Embeetle/tiny-scarab/documentation/website_figures/3d_render_02.webp

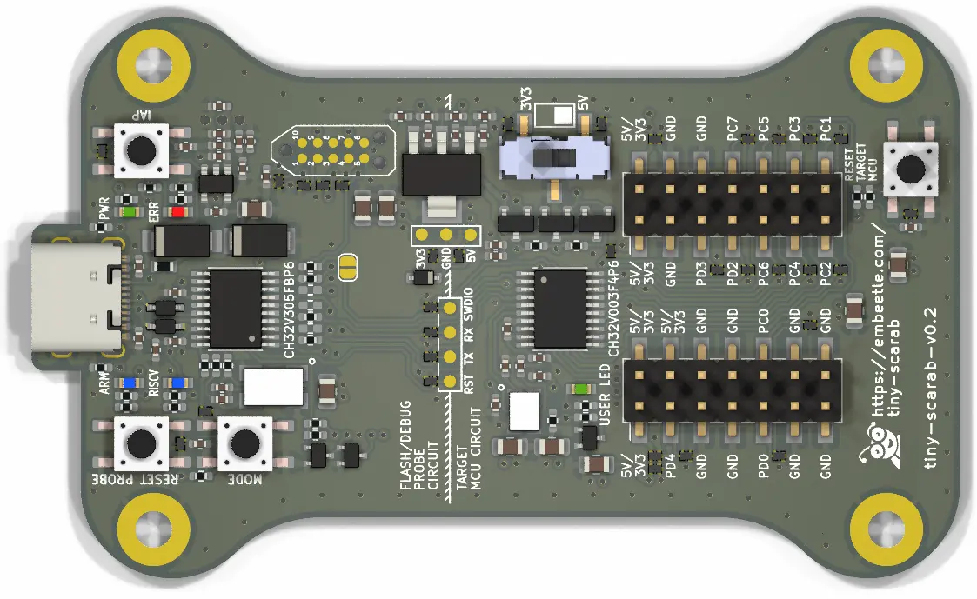
documentation/website_figures/3d_render_02.webp
