Embeetle/tiny-scarab/cardboard_box/box_dimensions.png

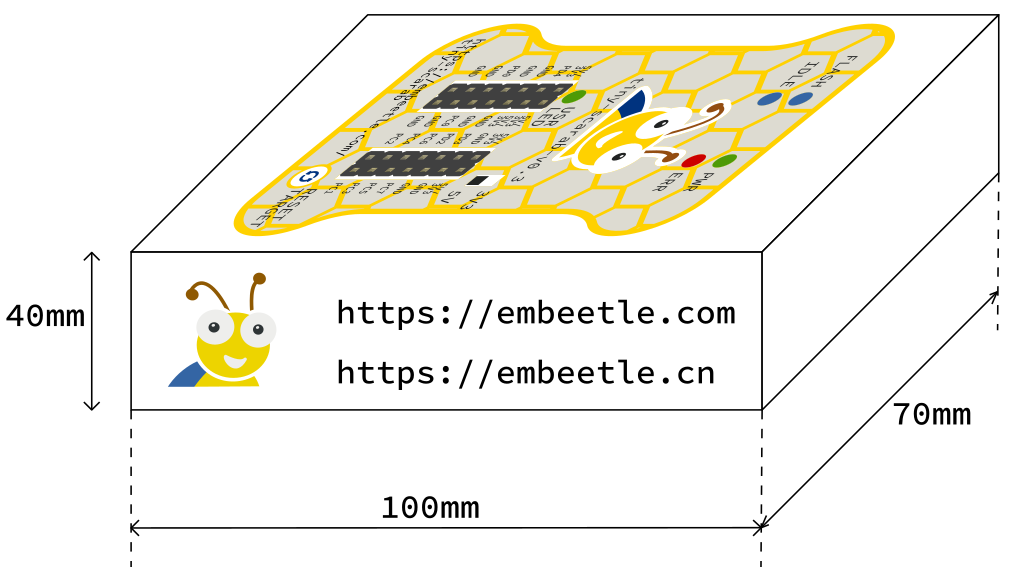
cardboard_box/box_dimensions.png
