Embeetle/tiny-scarab/cardboard_box/product_dimensions.png

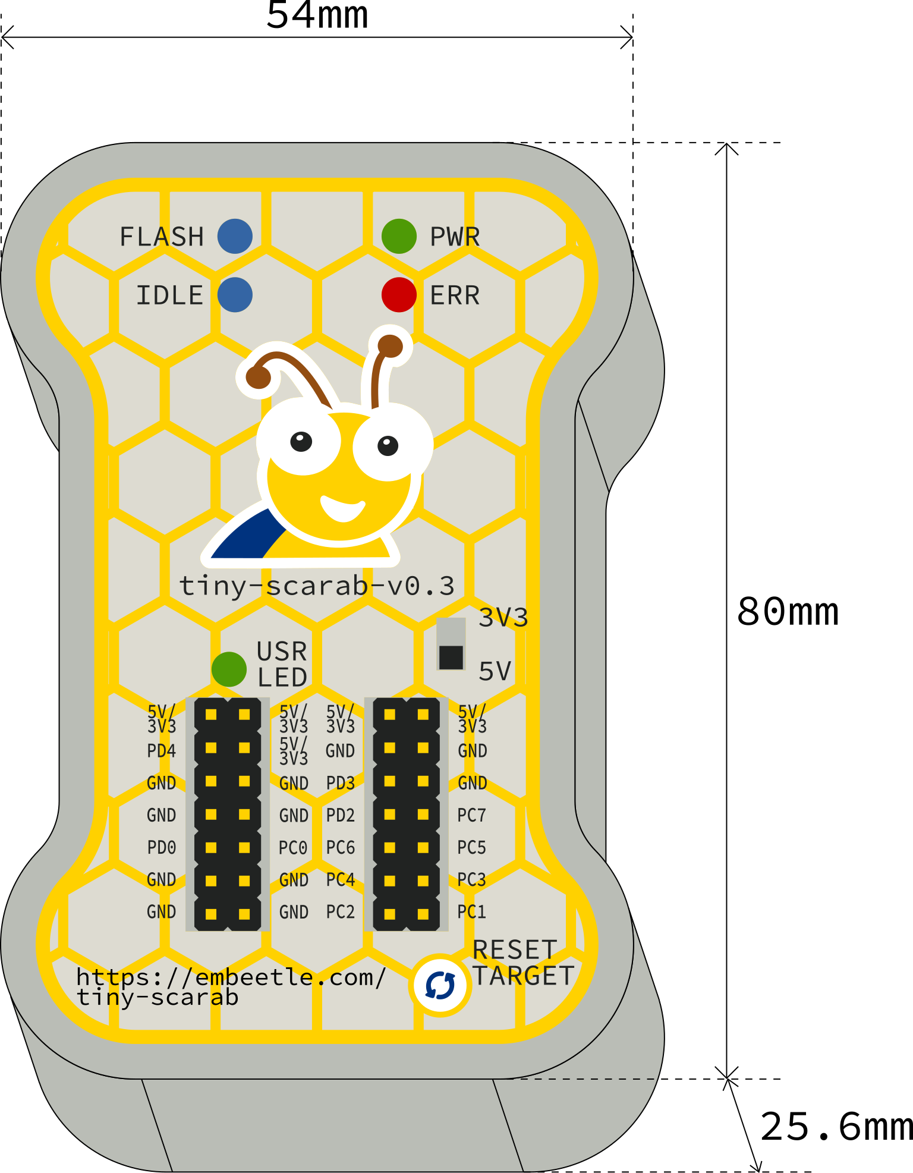
cardboard_box/product_dimensions.png
