Embeetle/tiny-scarab/cardboard_box/product_tree.png

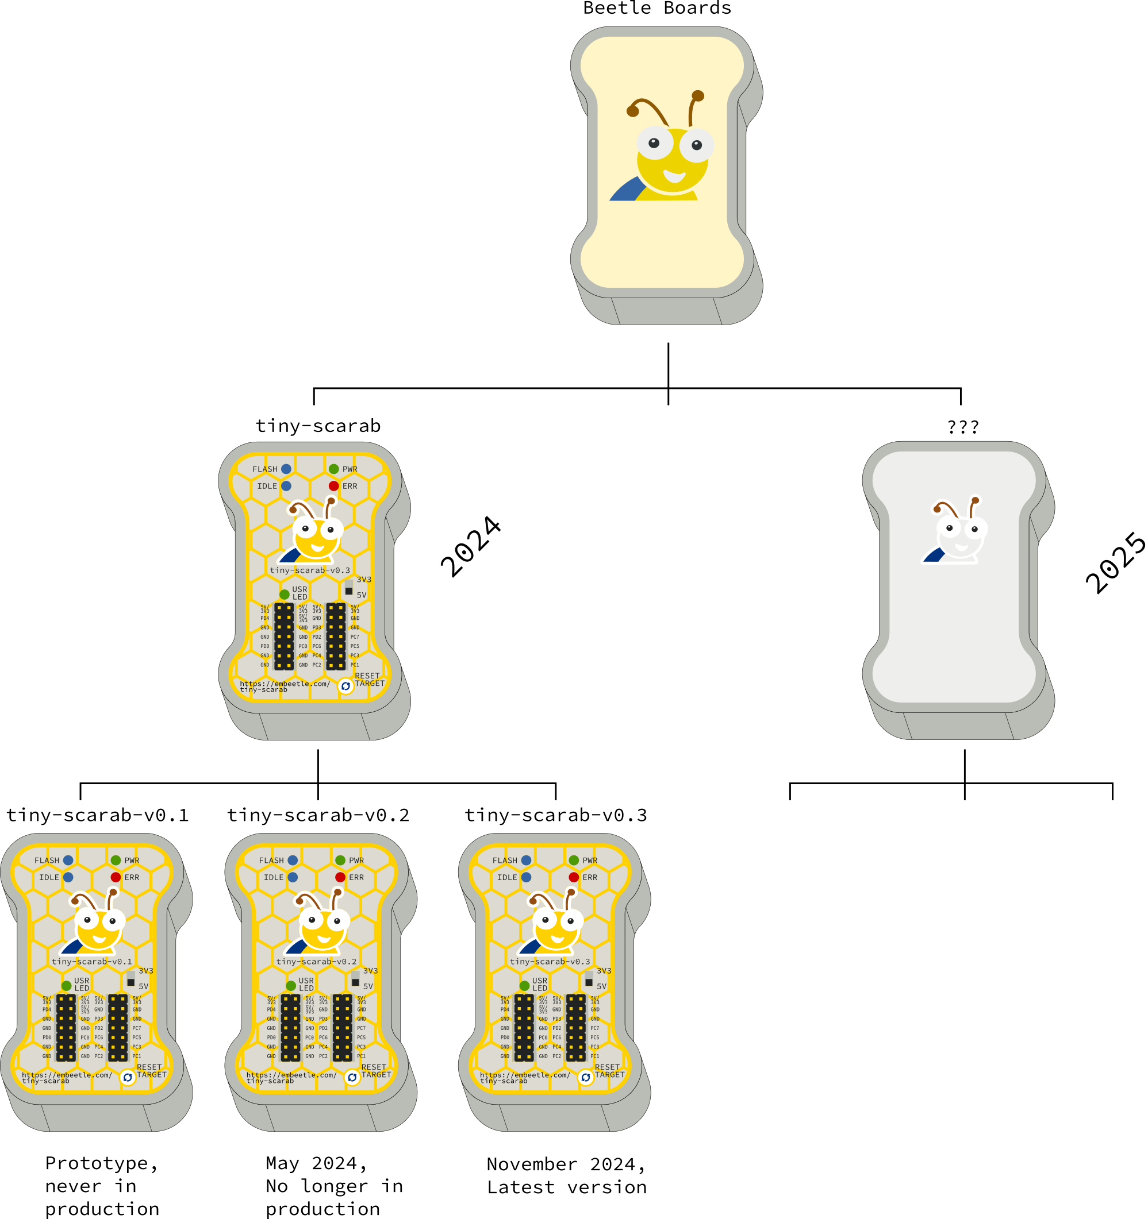
cardboard_box/product_tree.png
