Embeetle/tiny-scarab/cardboard_box/sides.png

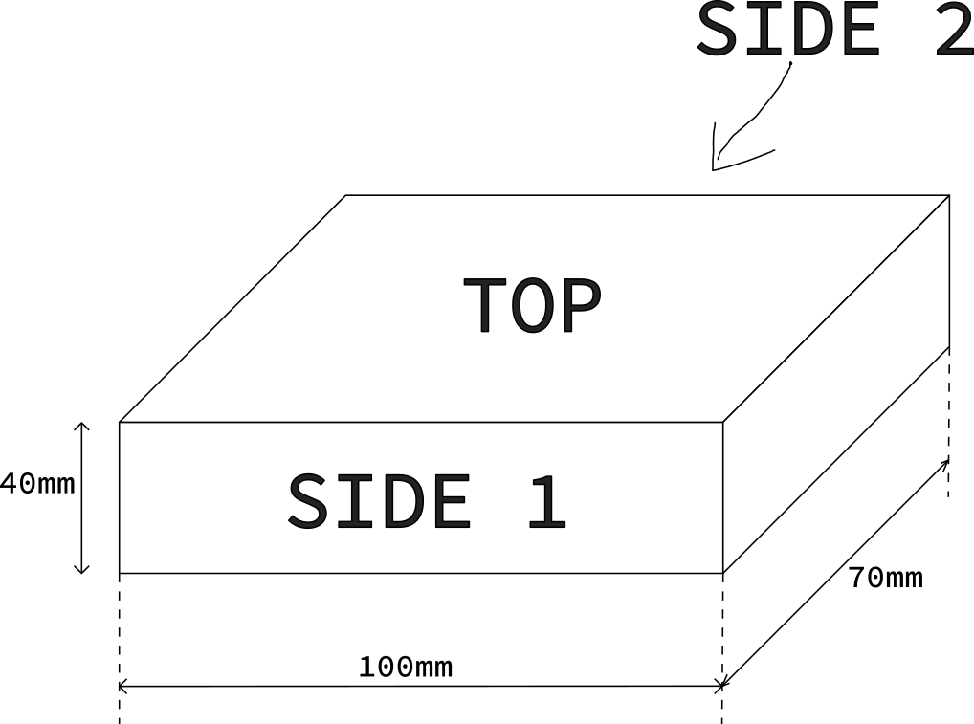
cardboard_box/sides.png
