Embeetle/tiny-scarab/documentation/3d_render_01.png

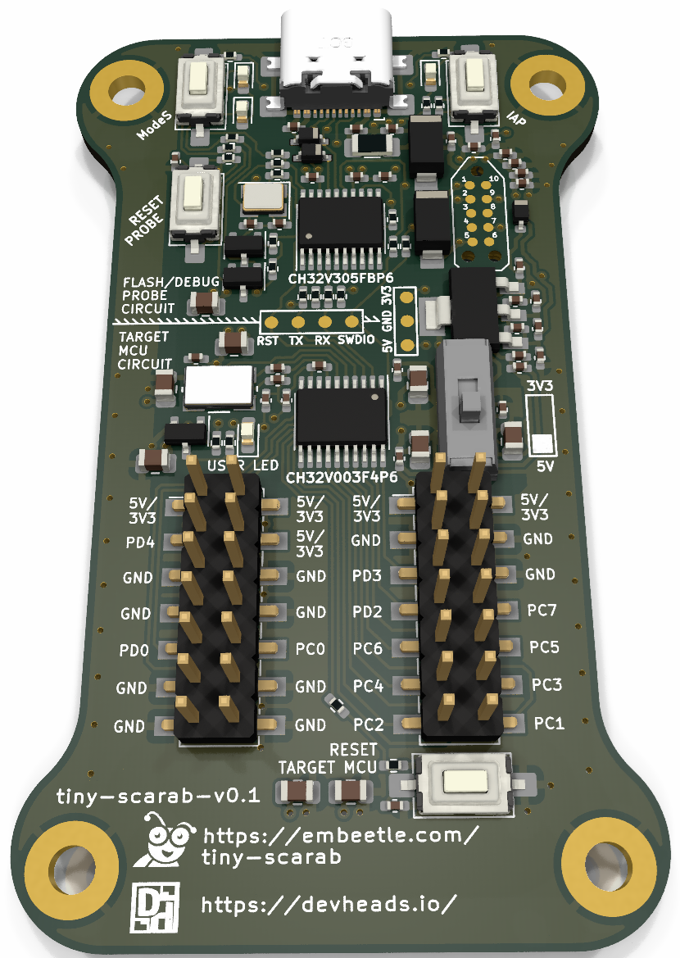
documentation/3d_render_01.png
