Embeetle/tiny-scarab/documentation/3d_render_02.png

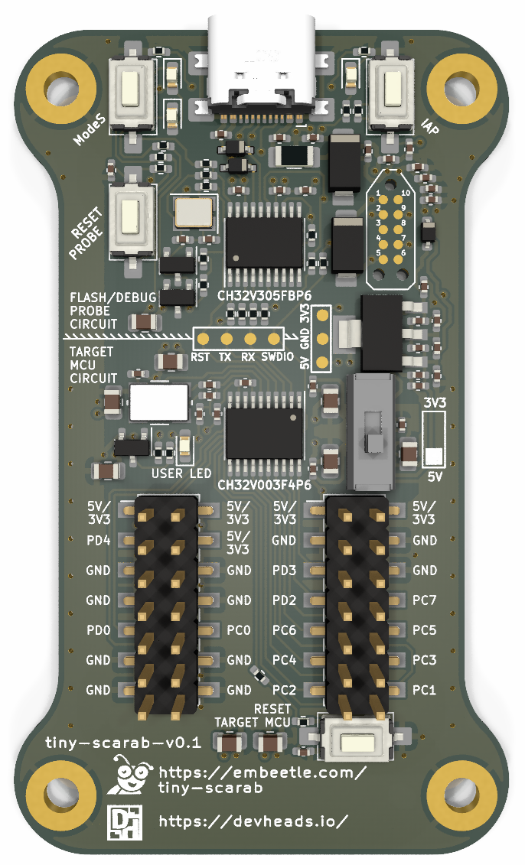
documentation/3d_render_02.png
