Embeetle/tiny-scarab/documentation/back.png

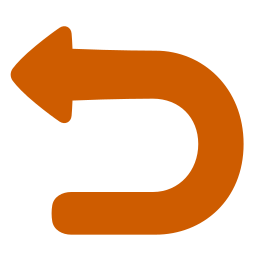
documentation/back.png
