Embeetle/tiny-scarab/documentation/drawing.png

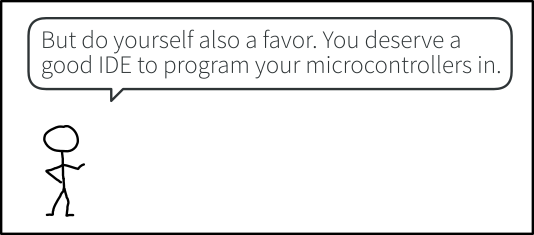
documentation/drawing.png
