Embeetle/tiny-scarab/documentation/esd_discharge_5V.png

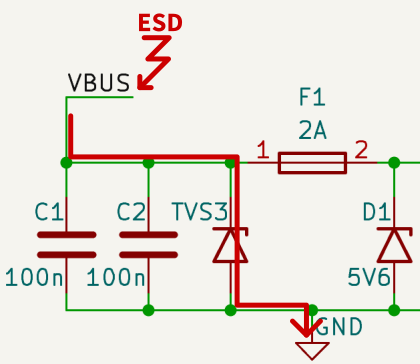
documentation/esd_discharge_5V.png
