Embeetle/tiny-scarab/documentation/files_explained_01.png

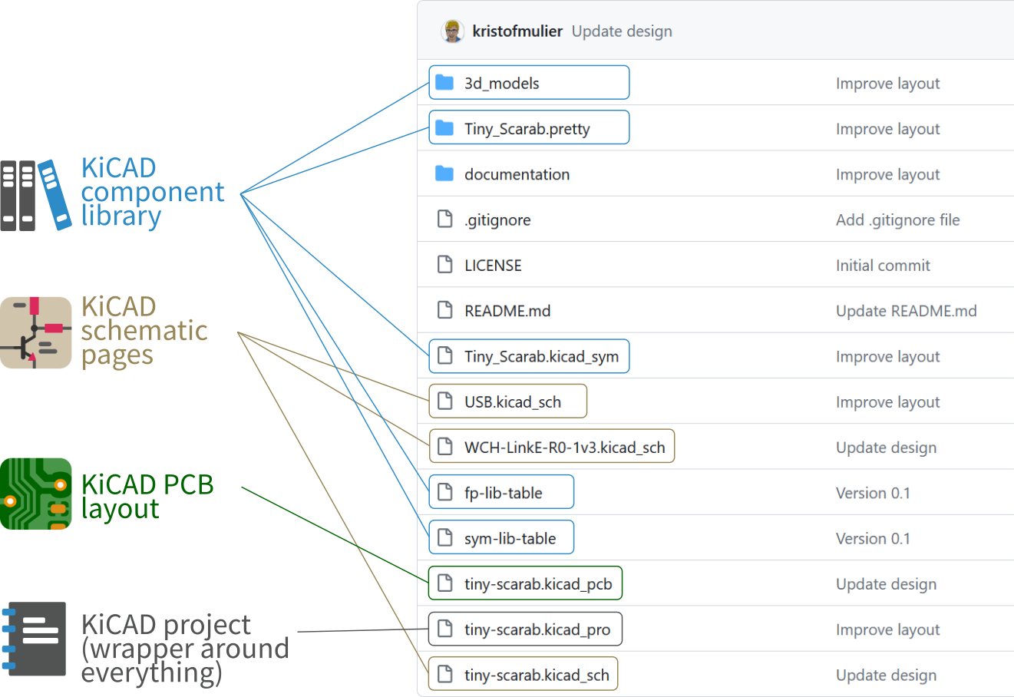
documentation/files_explained_01.png
