Embeetle/tiny-scarab/documentation/home.png

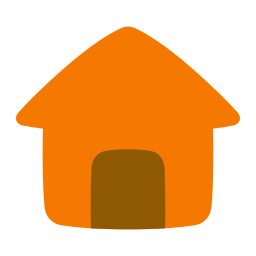
documentation/home.png
