Embeetle/tiny-scarab/documentation/open_project_01.png

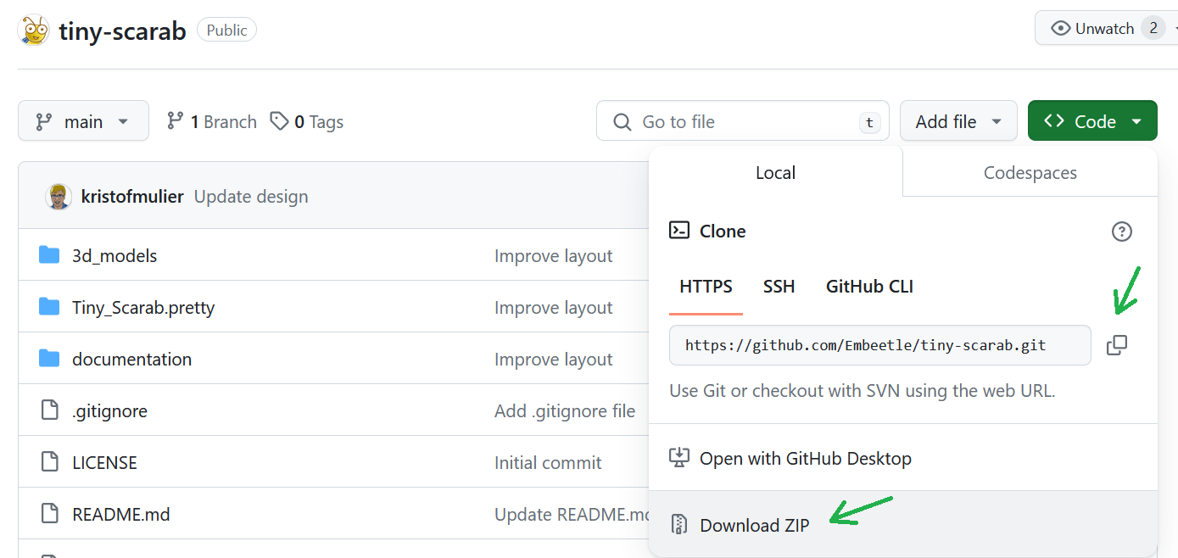
documentation/open_project_01.png
