Embeetle/tiny-scarab/documentation/open_project_02.png

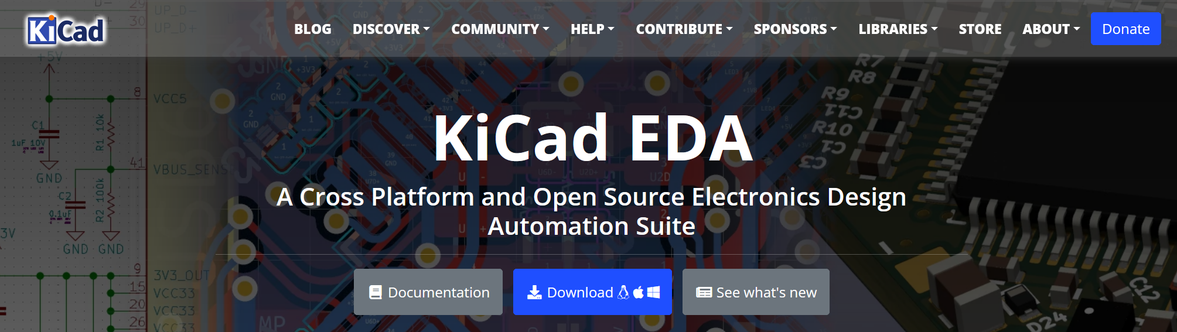
documentation/open_project_02.png
