Embeetle/tiny-scarab/documentation/open_project_03.png

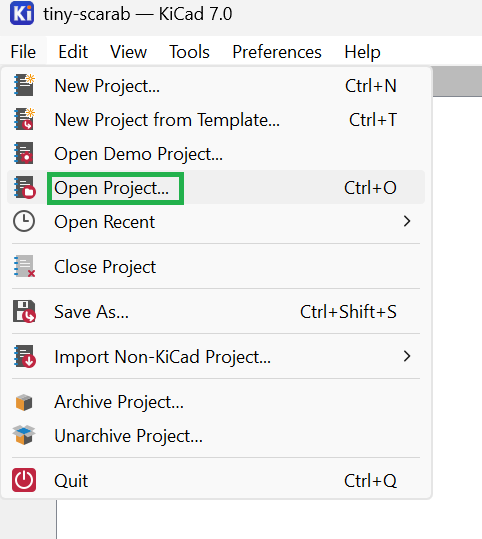
documentation/open_project_03.png
