Embeetle/tiny-scarab/documentation/open_project_04.png

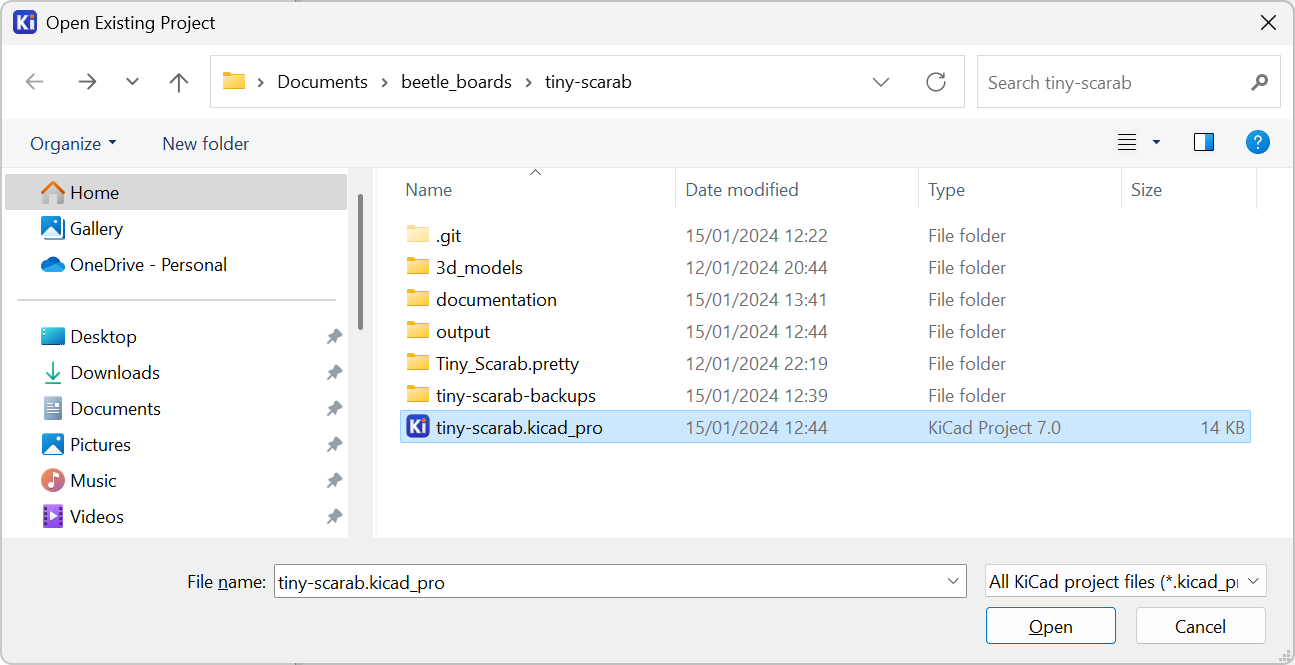
documentation/open_project_04.png
