Embeetle/tiny-scarab/documentation/open_project_05.png

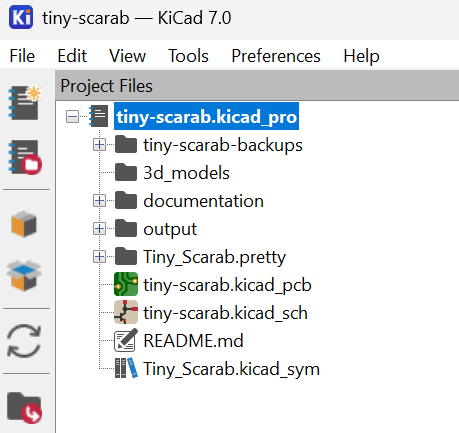
documentation/open_project_05.png
