Embeetle/tiny-scarab/documentation/short_circuit.png

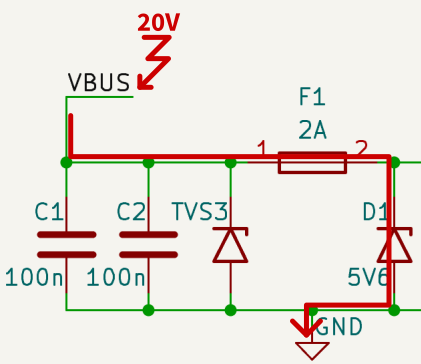
documentation/short_circuit.png
