Embeetle/tiny-scarab/documentation/tiny-scarab.png

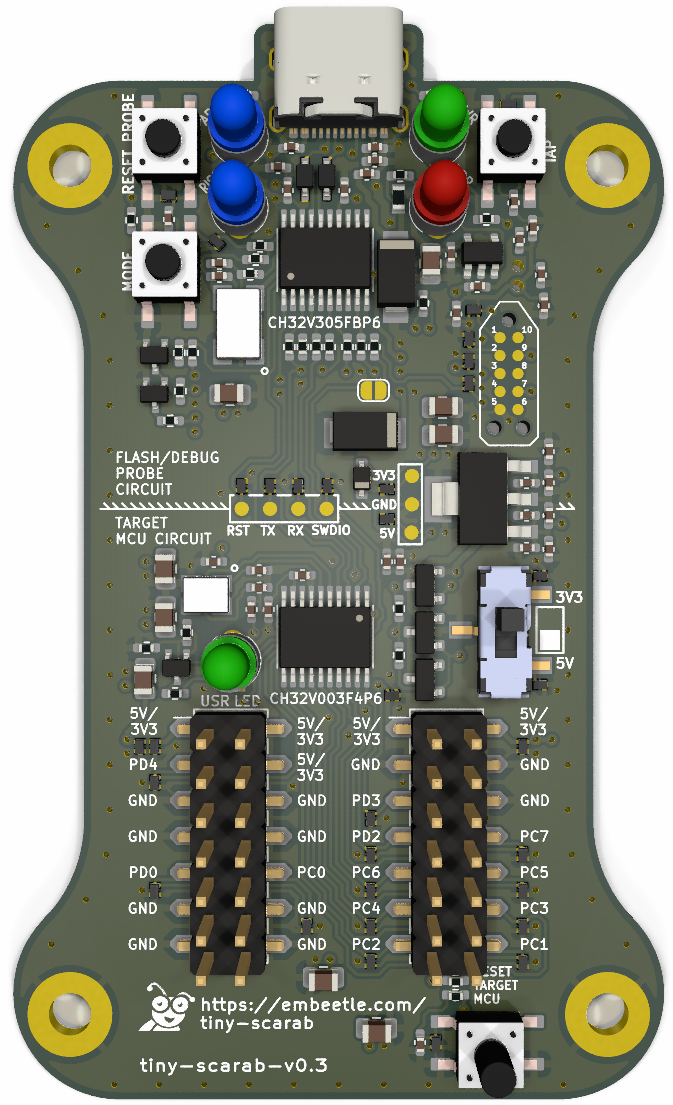
documentation/tiny-scarab.png
