Embeetle/tiny-scarab/documentation/website_figures/3d_render_01.png

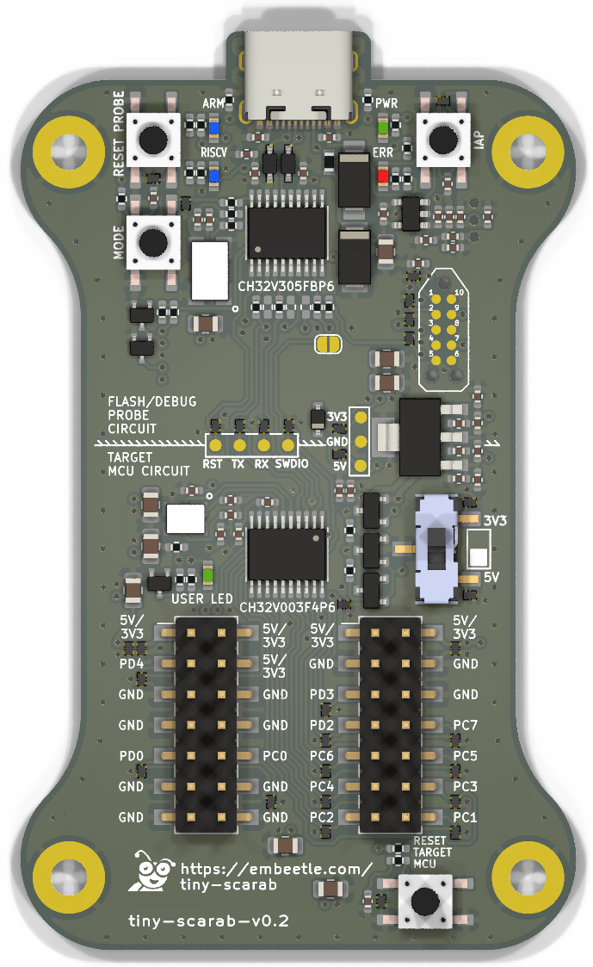
documentation/website_figures/3d_render_01.png
