Embeetle/tiny-scarab/documentation/website_figures/connections_01.webp

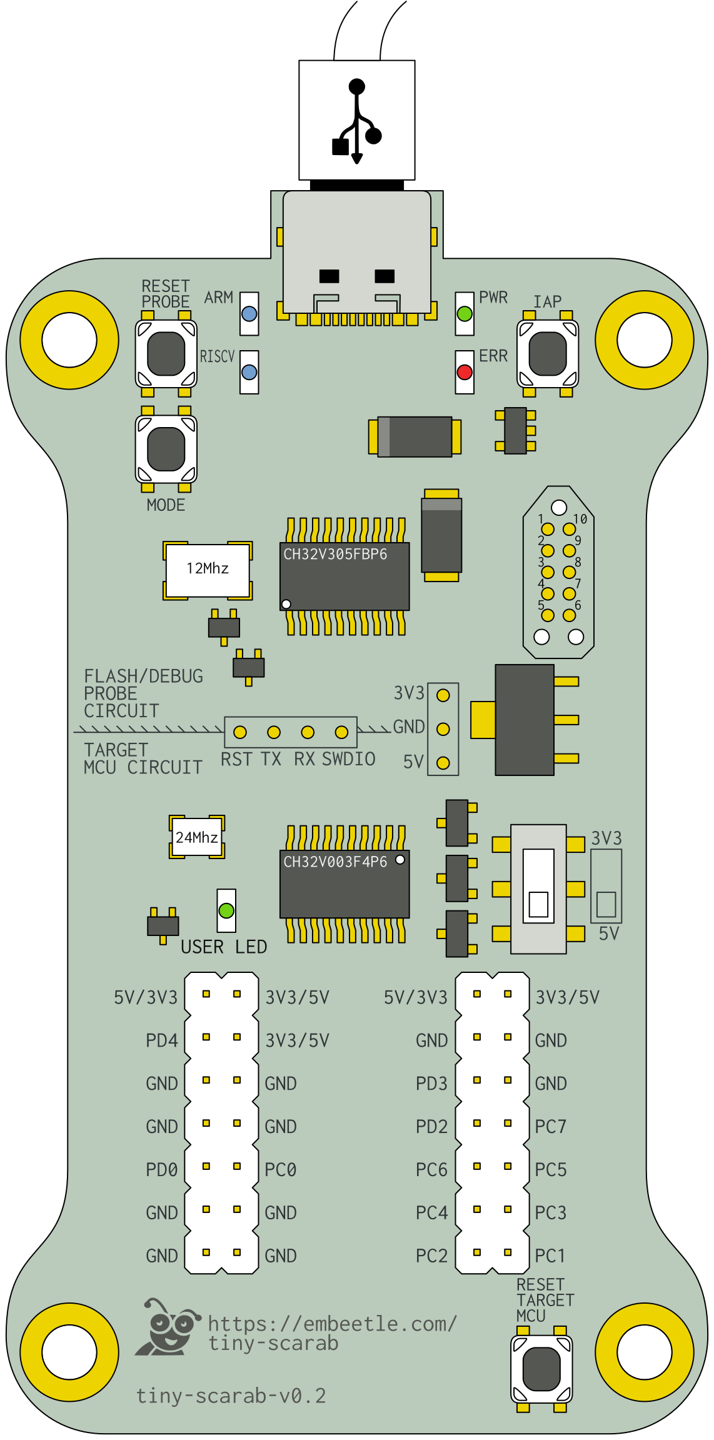
documentation/website_figures/connections_01.webp
