Embeetle/tiny-scarab/documentation/website_figures/mcu_photo.png

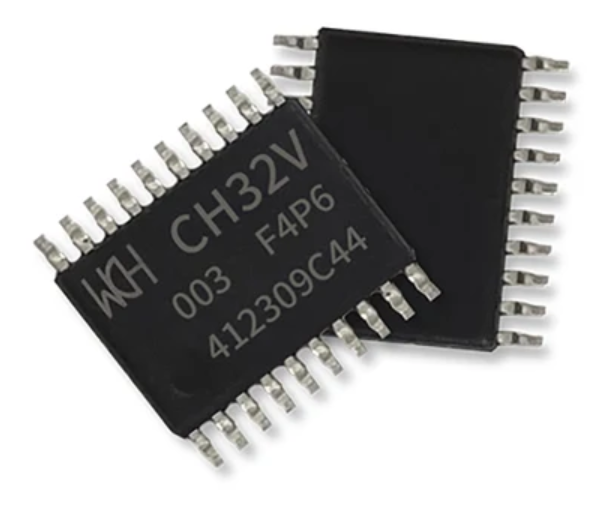
documentation/website_figures/mcu_photo.png
