Embeetle/tiny-scarab/documentation/website_figures/photo_01.webp

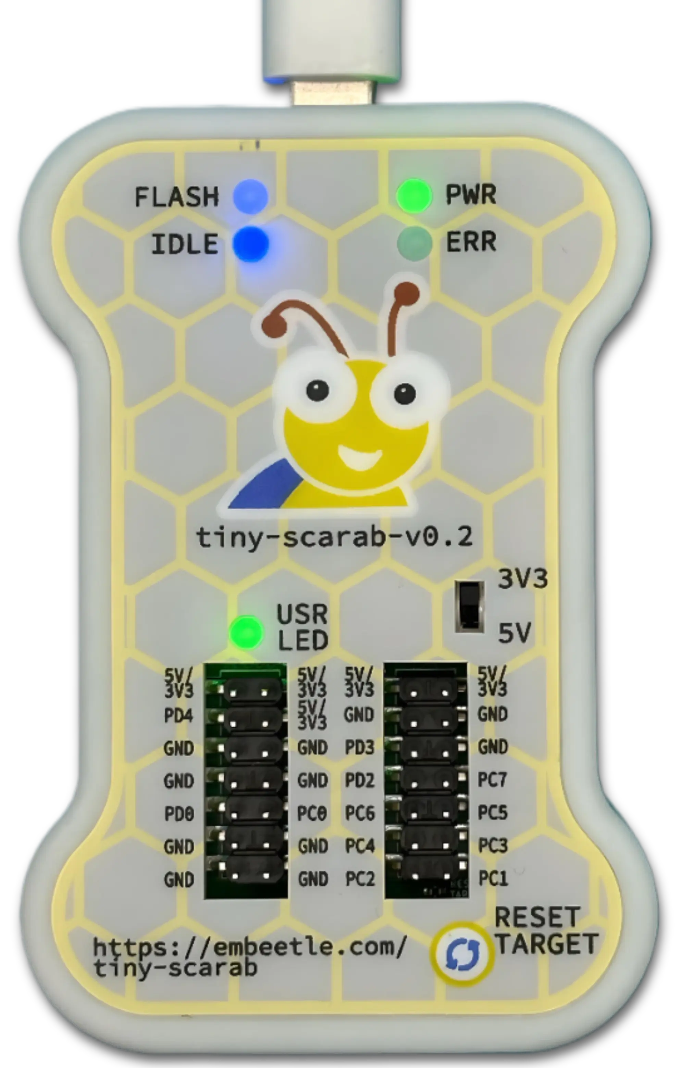
documentation/website_figures/photo_01.webp
