Embeetle/tiny-scarab/documentation/website_figures/photo_02.webp

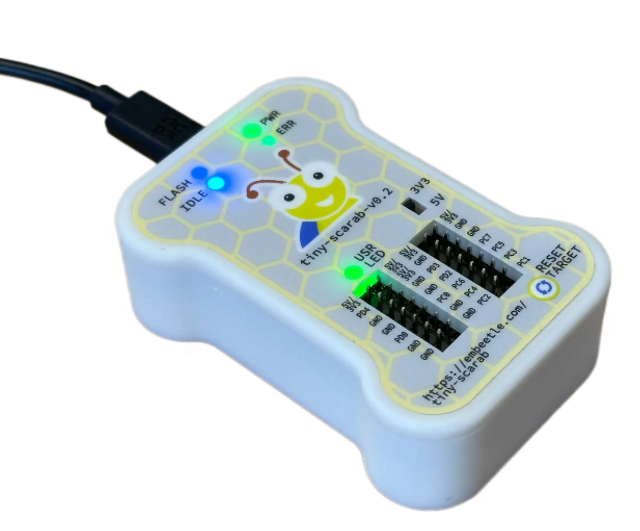
documentation/website_figures/photo_02.webp
