Embeetle/tiny-scarab/documentation/website_figures/photo_03.webp

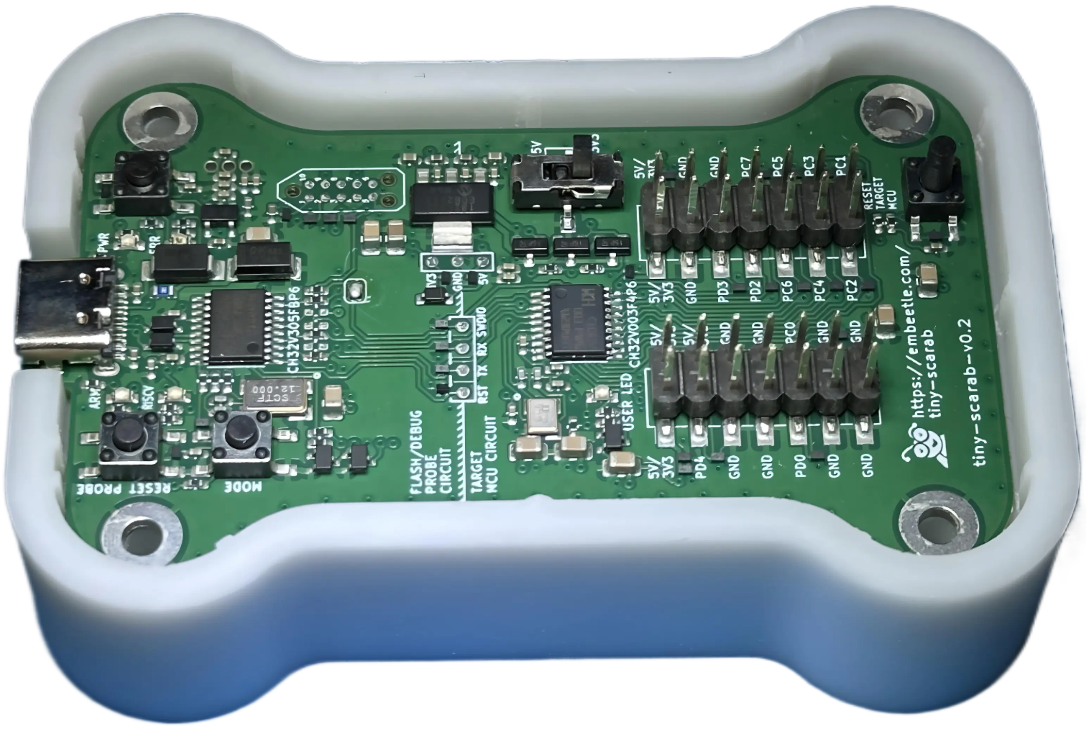
documentation/website_figures/photo_03.webp
