Embeetle/tiny-scarab/documentation/website_figures/photo_04.png

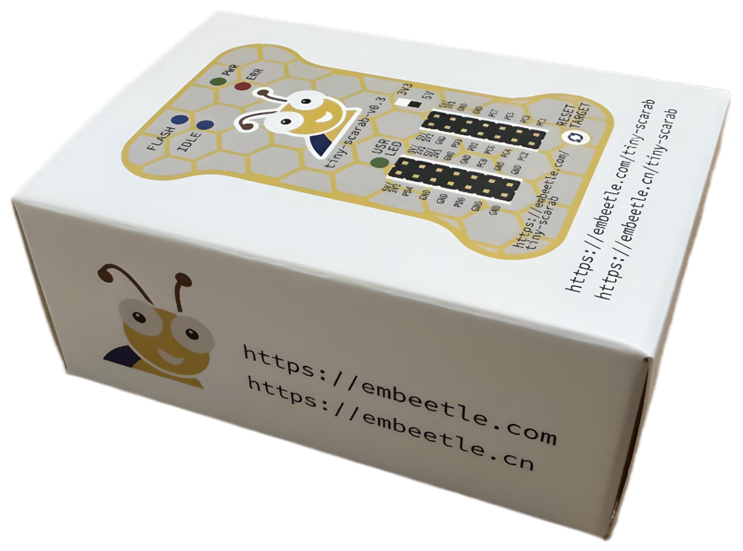
documentation/website_figures/photo_04.png
