Embeetle/tiny-scarab/documentation/website_figures/photo_05.png

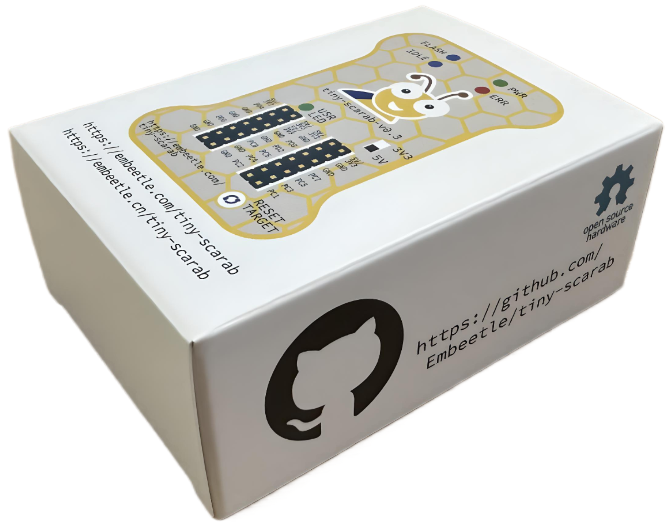
documentation/website_figures/photo_05.png
