Embeetle/tiny-scarab/documentation/website_figures/power_protection_01.png

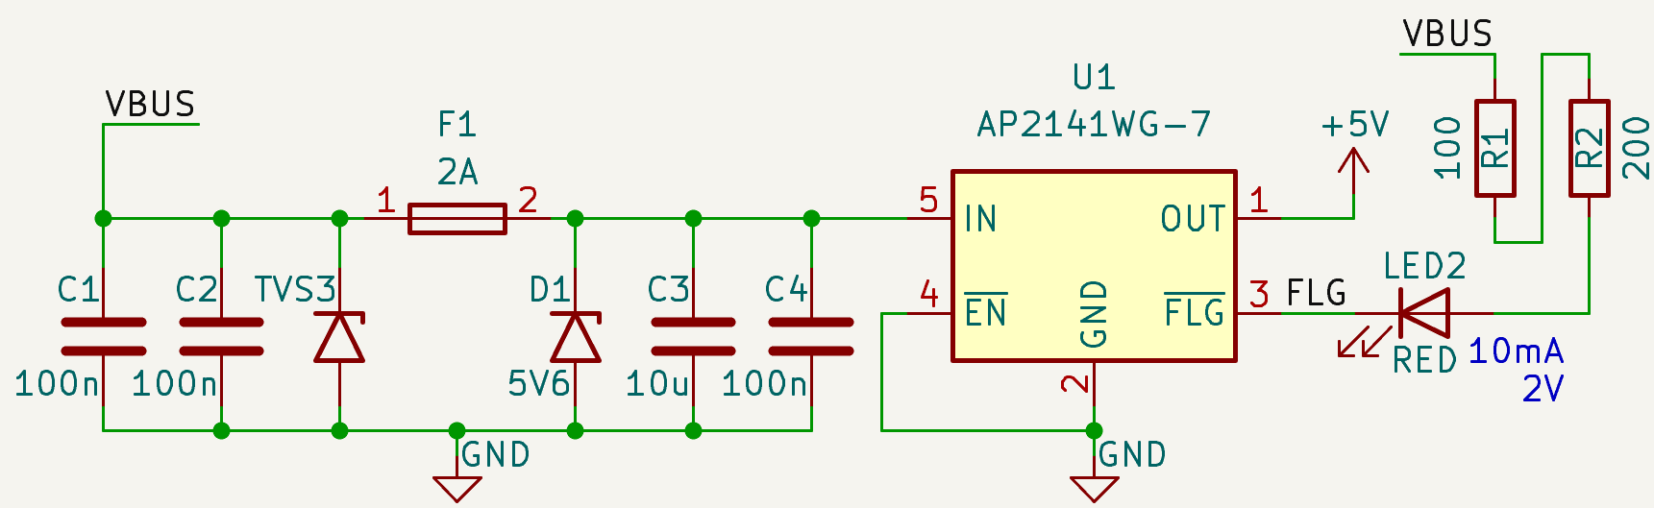
documentation/website_figures/power_protection_01.png
