Embeetle/tiny-scarab/documentation/website_figures/screenshot.png

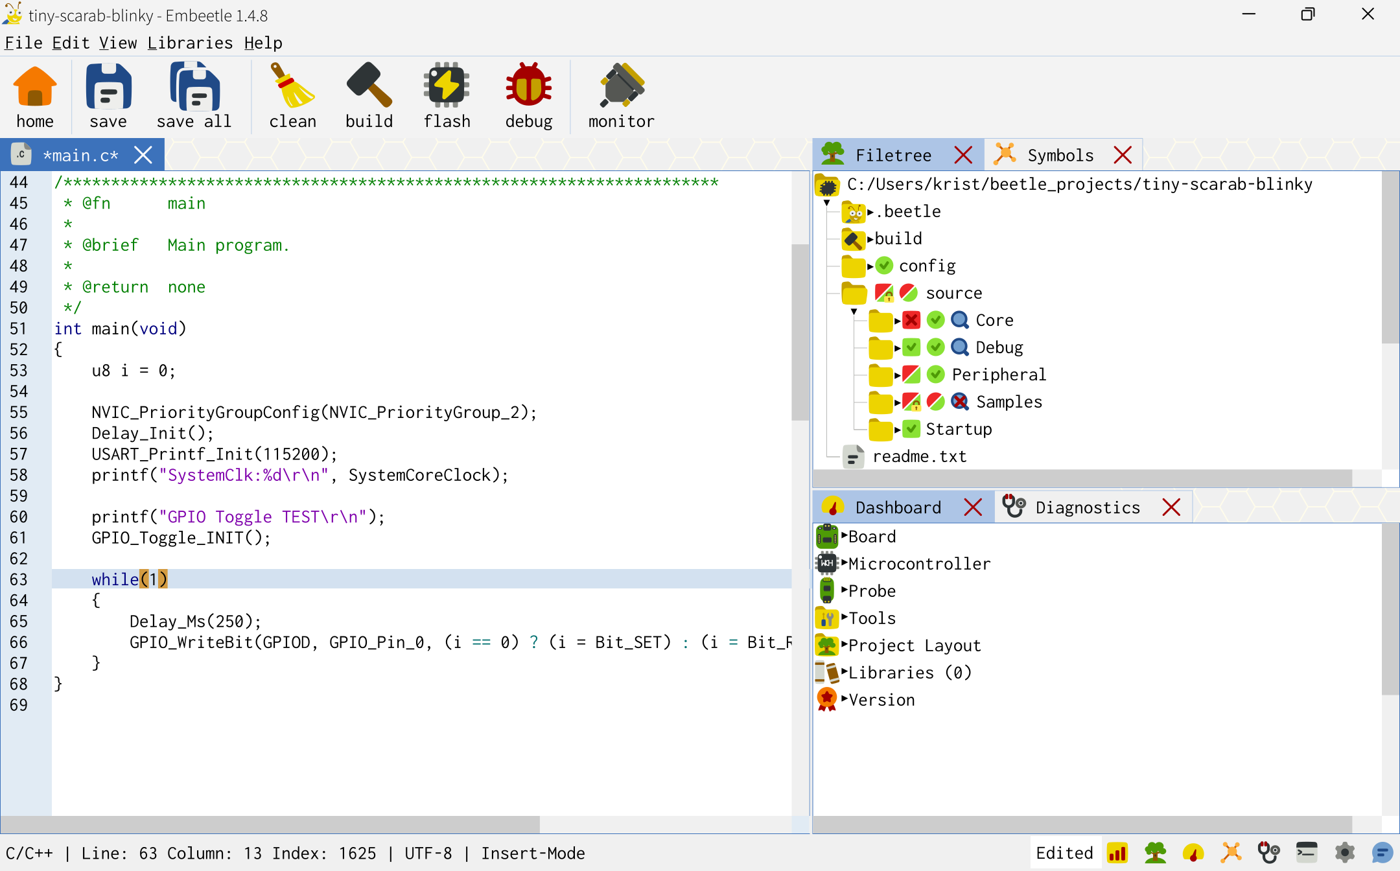
documentation/website_figures/screenshot.png
