Embeetle/tiny-scarab/documentation/website_figures/tiny_scarab_with_screenshot.png

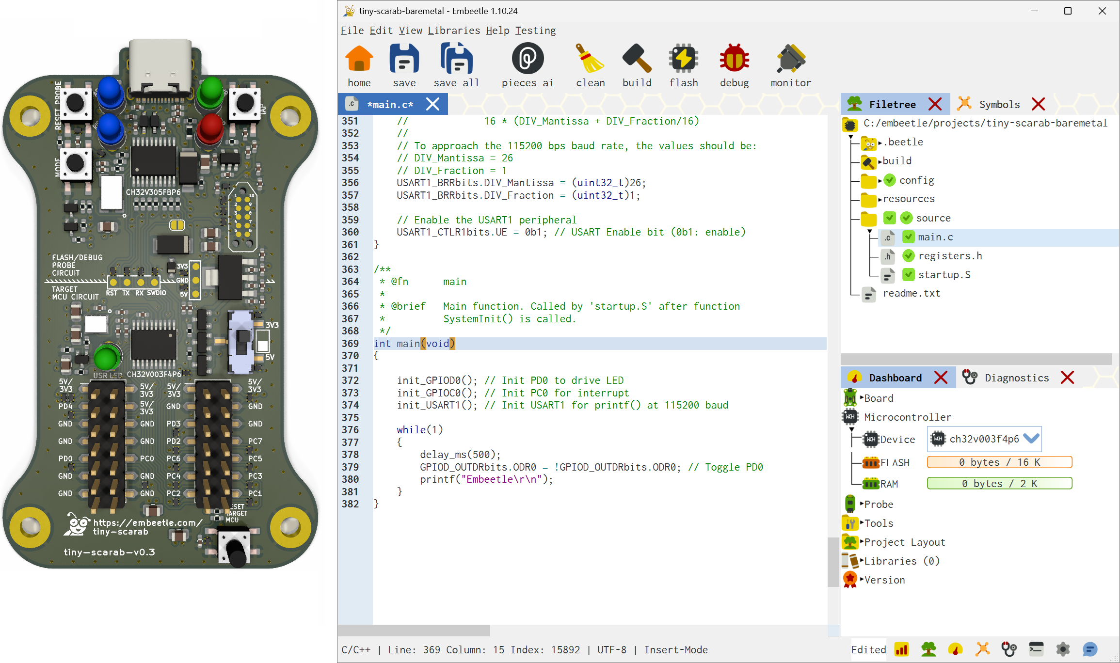
documentation/website_figures/tiny_scarab_with_screenshot.png
