Embeetle/tiny-scarab/documentation/website_figures/voltage_conversion_01.png

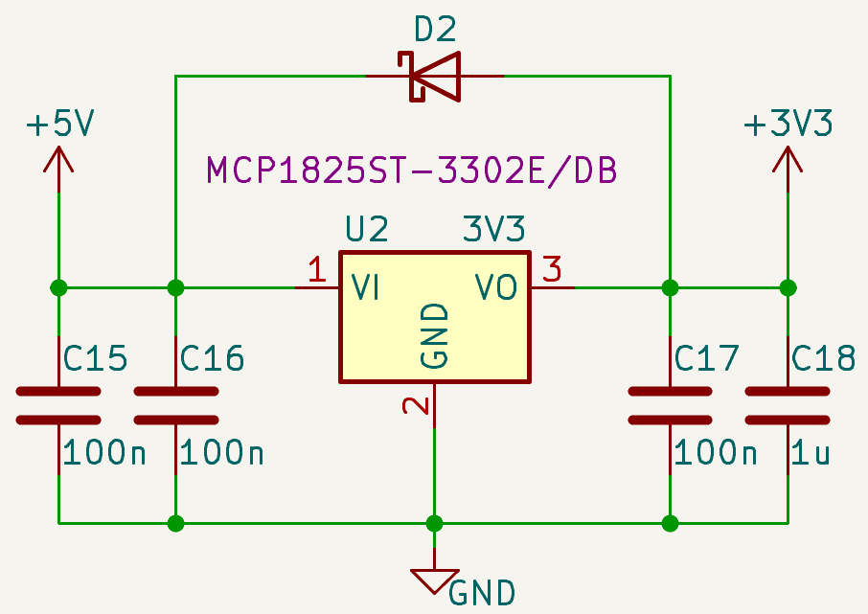
documentation/website_figures/voltage_conversion_01.png
