Embeetle/tiny-scarab/enclosure/screws.png

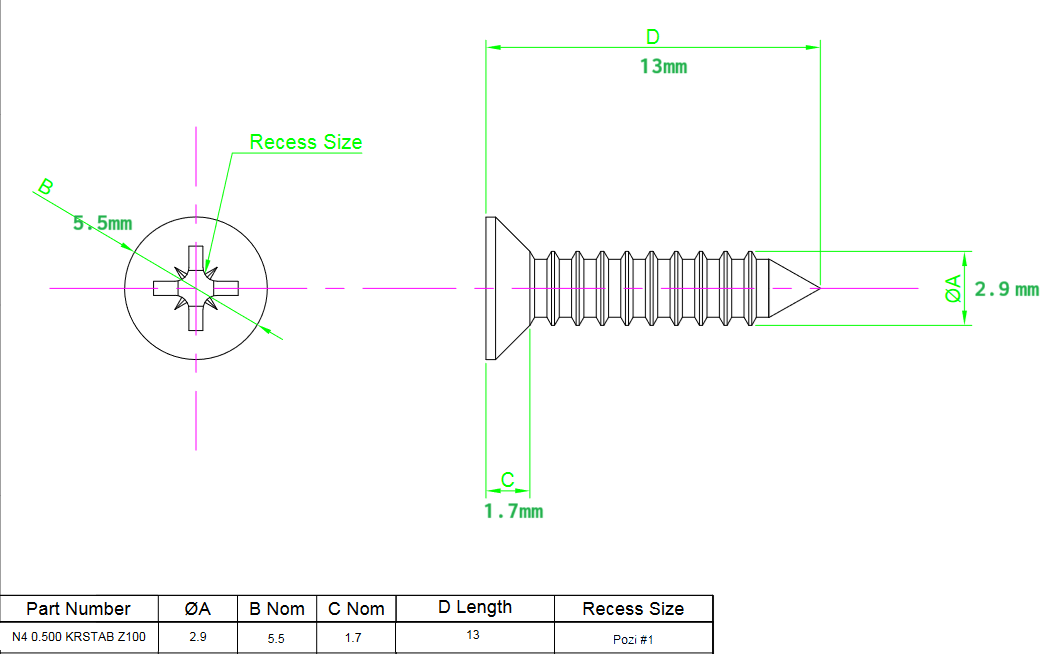
enclosure/screws.png
