Embeetle/tiny-scarab/graphic_overlay/button.png

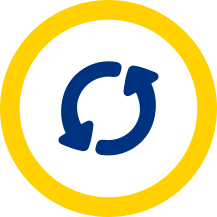
graphic_overlay/button.png
