Embeetle/tiny-scarab/graphic_overlay/profiles/pushbutton_profile.png

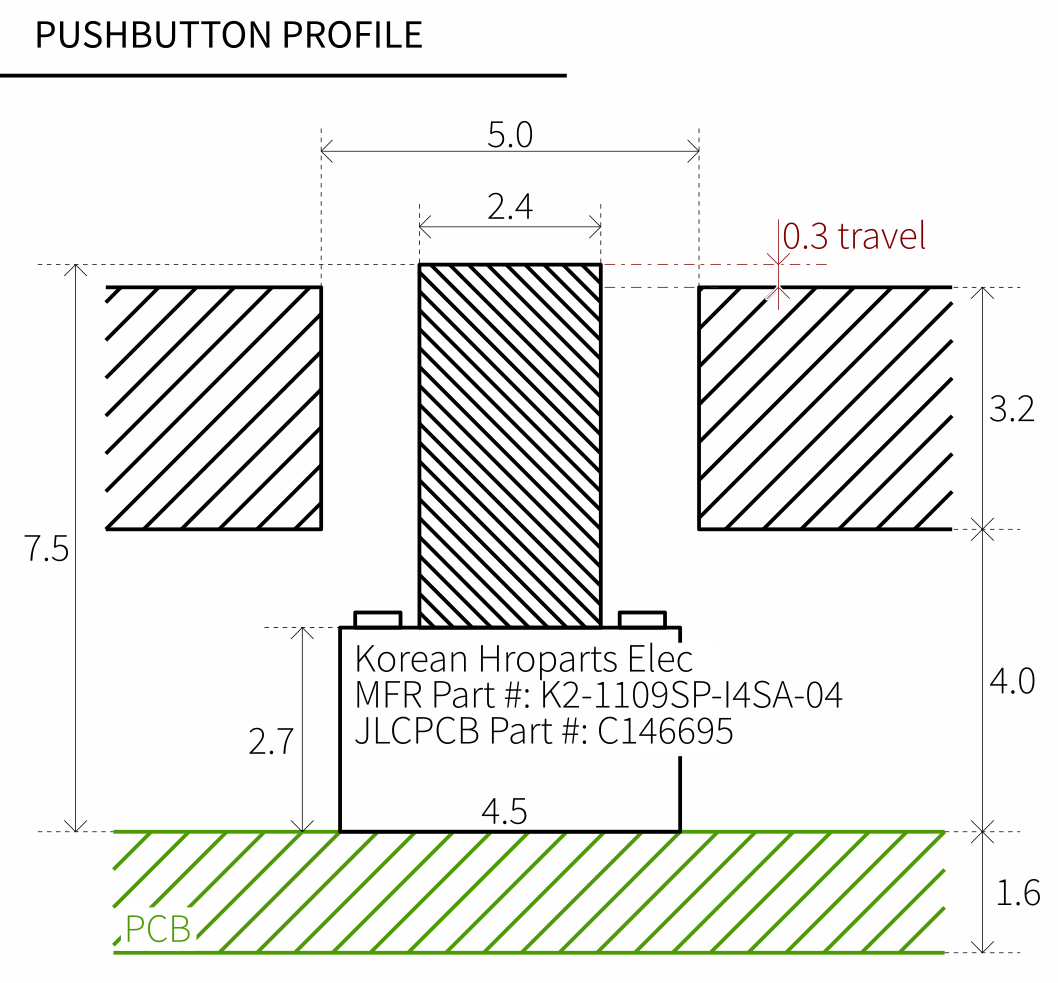
graphic_overlay/profiles/pushbutton_profile.png
