Embeetle/tiny-scarab/graphic_overlay/profiles/pushbutton_profile_01.png

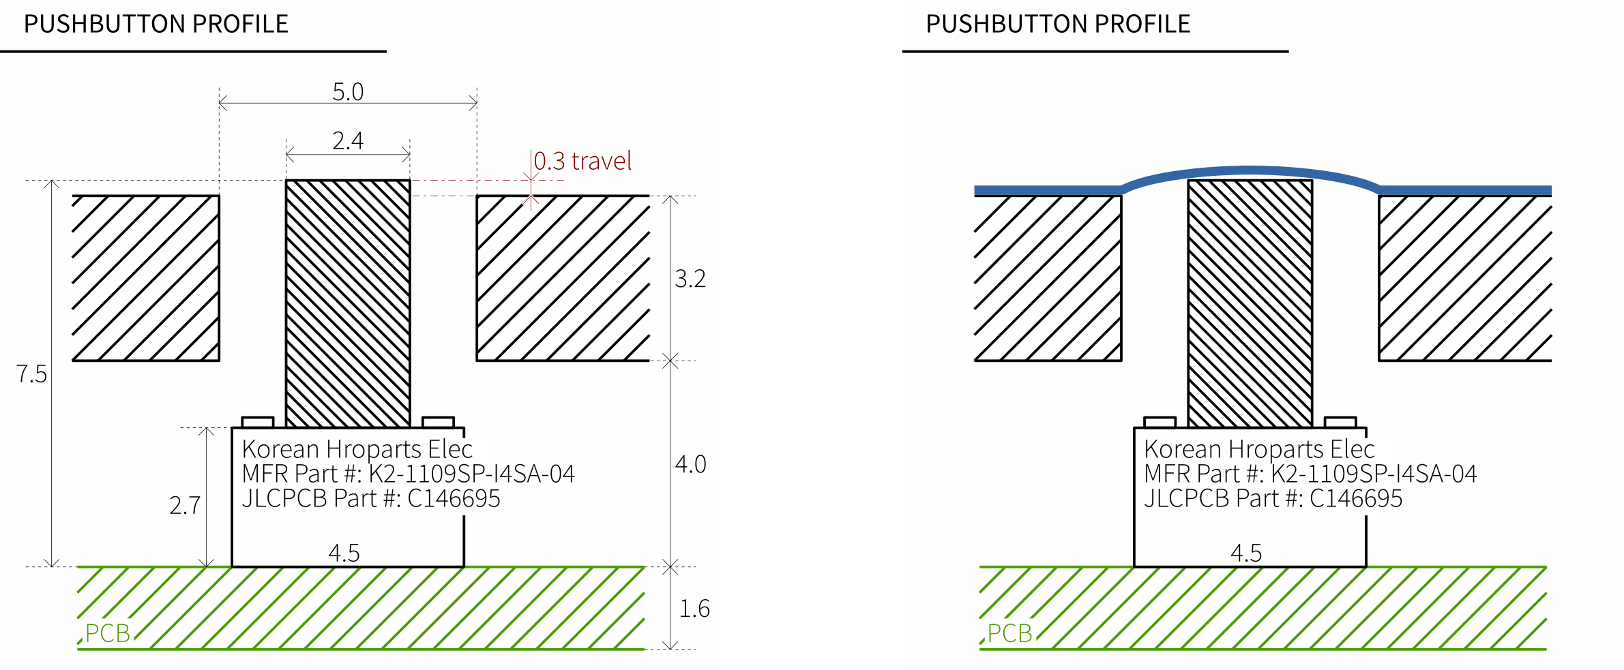
graphic_overlay/profiles/pushbutton_profile_01.png
