Embeetle/tiny-scarab/production/led_profile.png

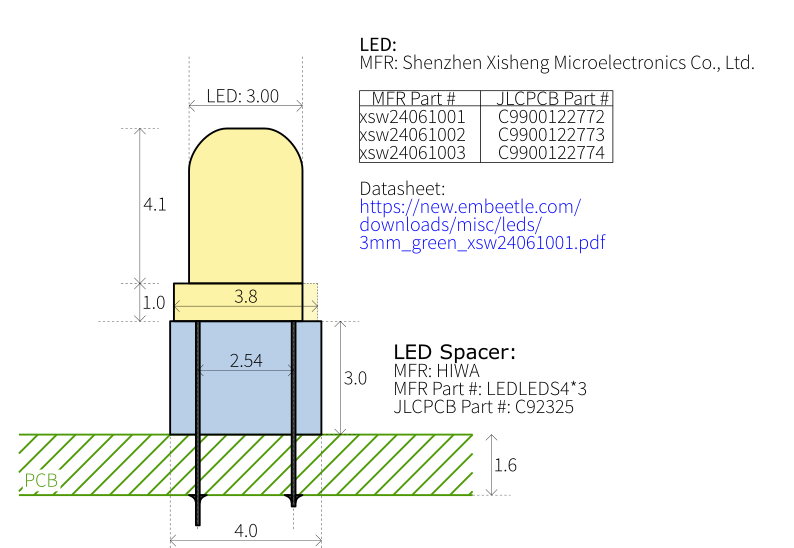
production/led_profile.png
