Embeetle/tiny-scarab/documentation/suppliers_screws_and_blocks.jpg

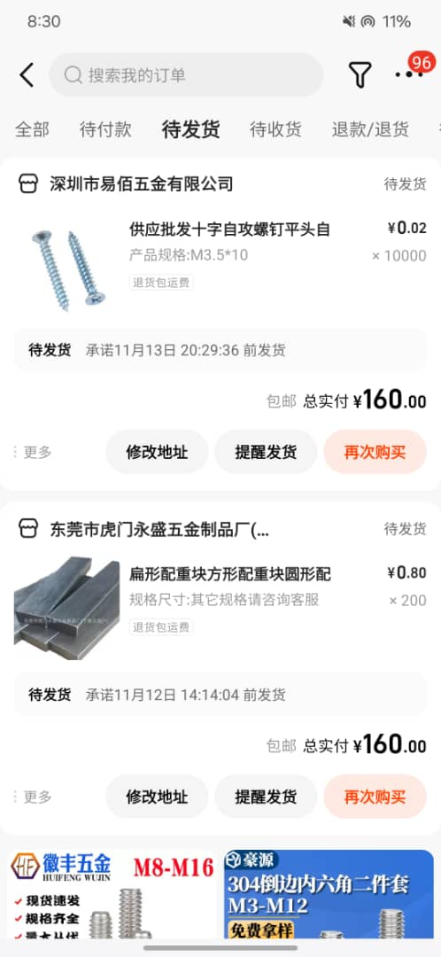
documentation/suppliers_screws_and_blocks.jpg
