Embeetle/tiny-scarab/production/order_screenshot_01.png

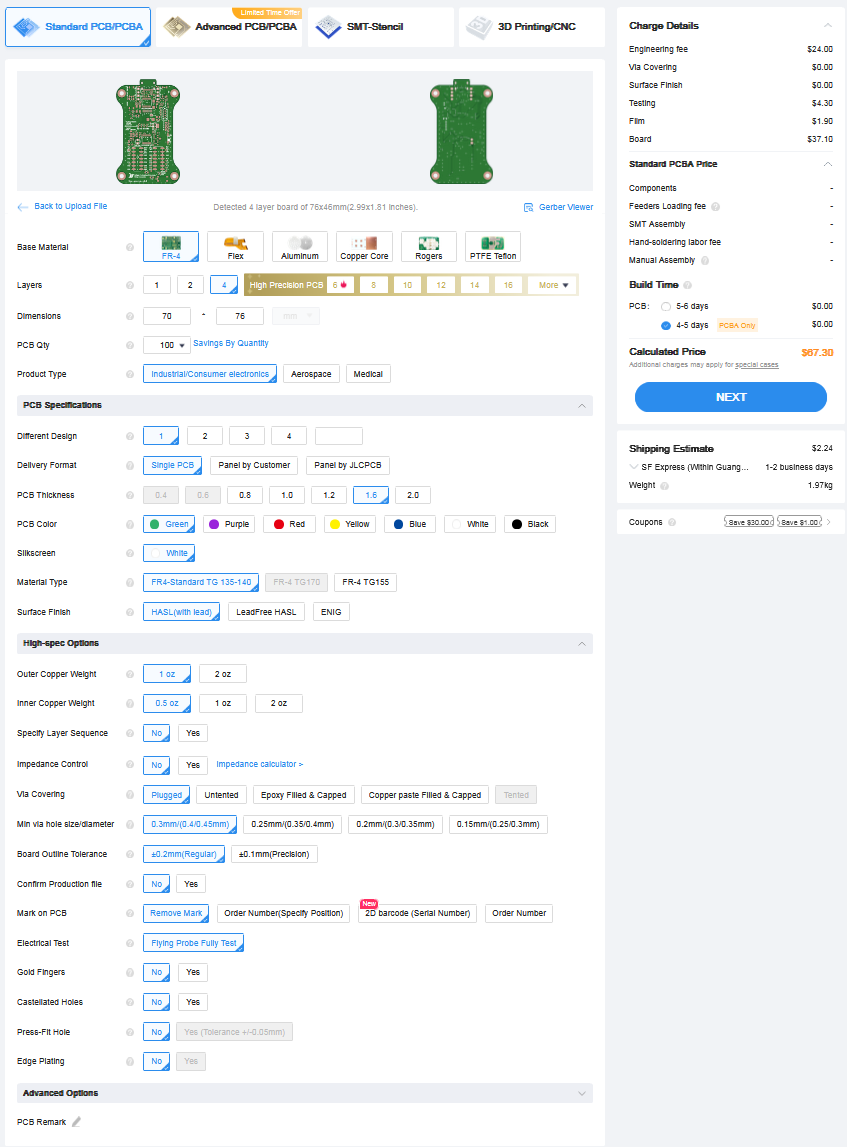
production/order_screenshot_01.png
