Embeetle/tiny-scarab/production/order_screenshot_02.png

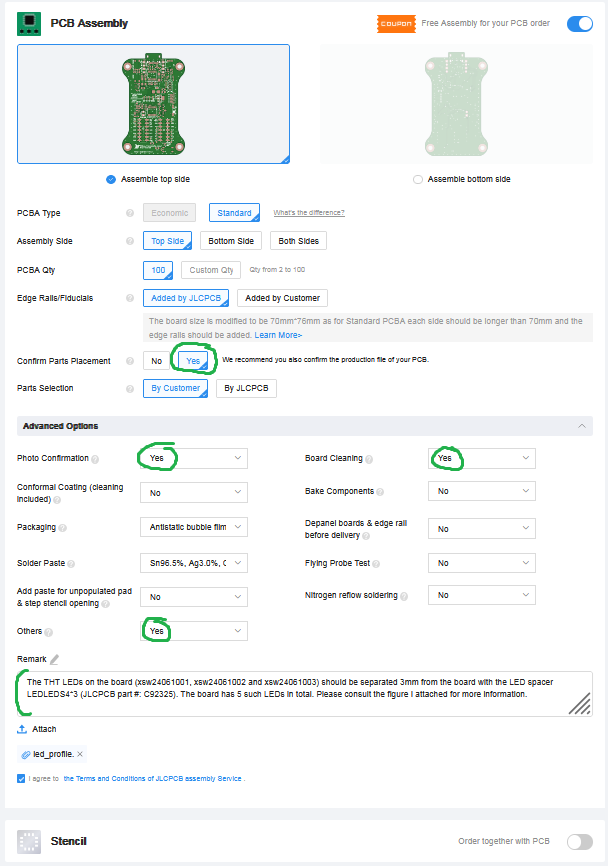
production/order_screenshot_02.png
