Embeetle/tiny-scarab/production/order_screenshot_03.png

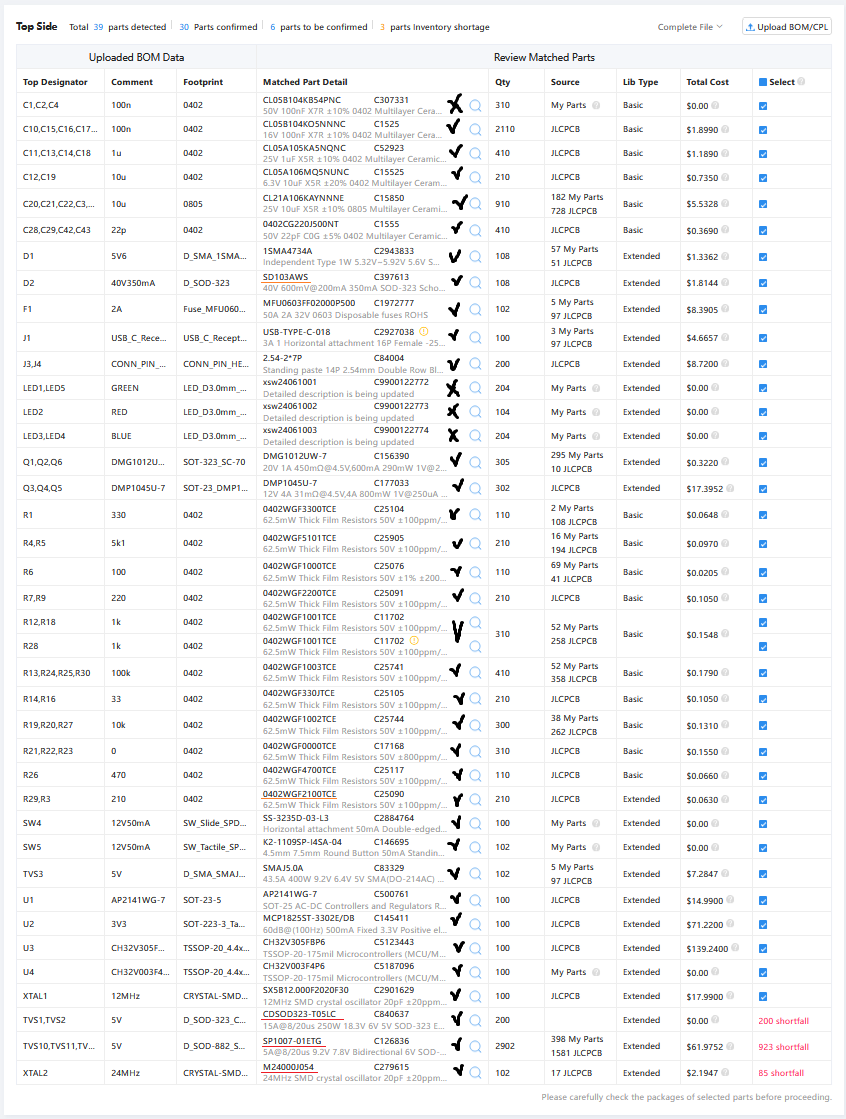
production/order_screenshot_03.png
