Embeetle/tiny-scarab/production/order_screenshot_04.png

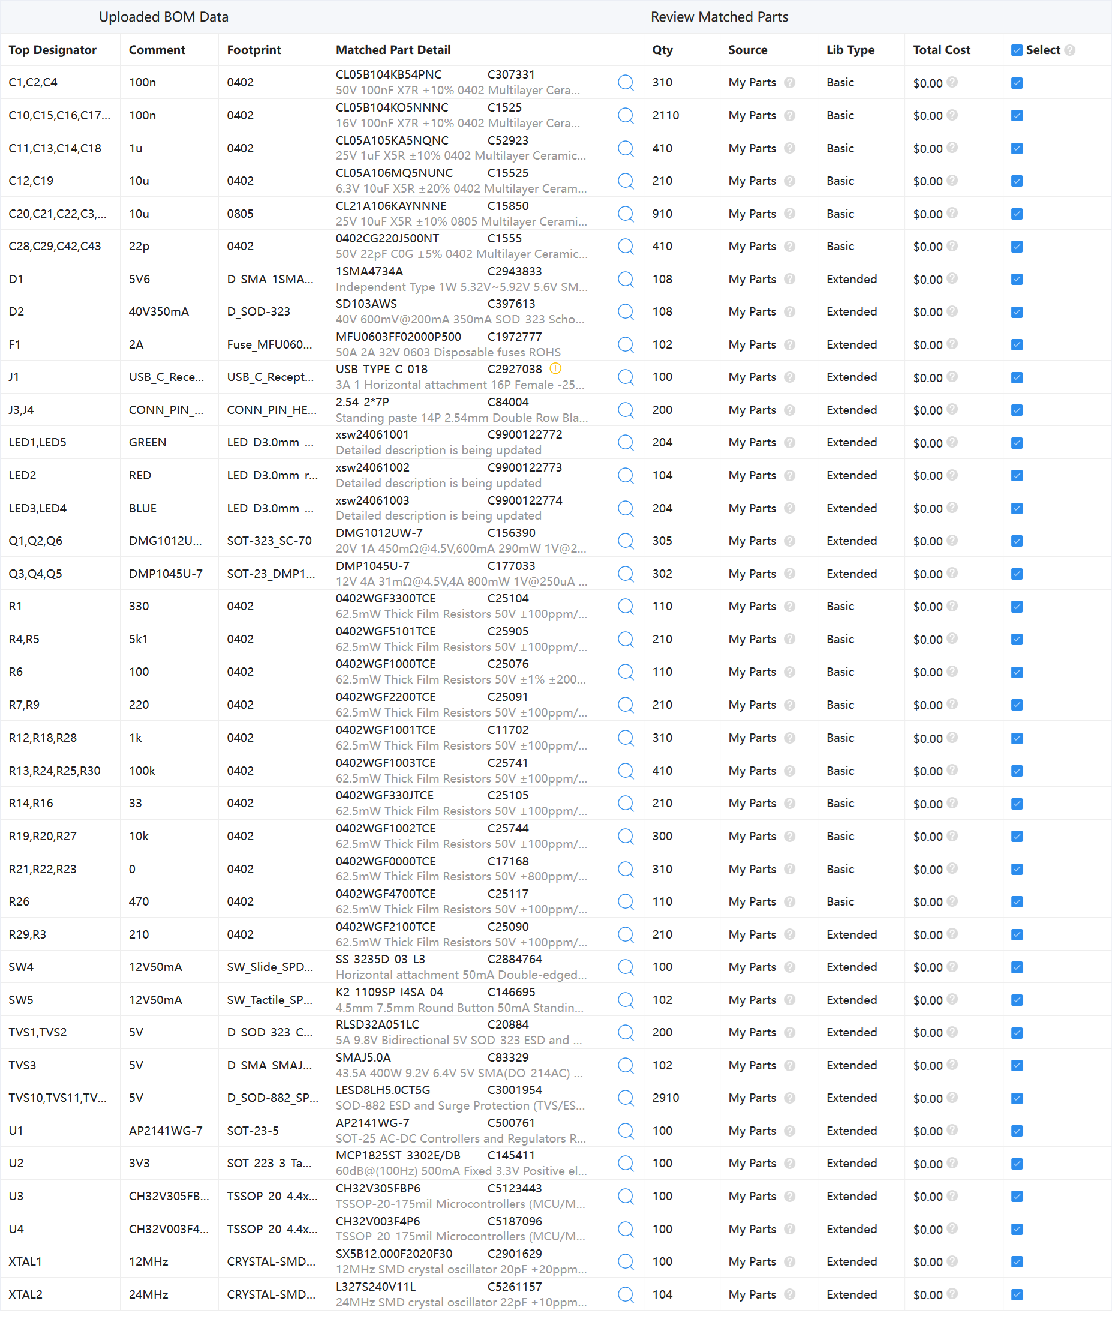
production/order_screenshot_04.png
