Embeetle/tiny-scarab/3d_models/alpsalpine_skrp.stp

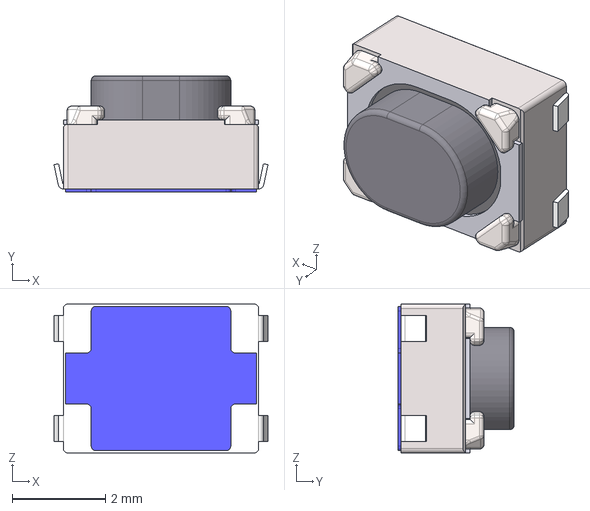
[picture p125: CAD file, 2024-01-21]
3d_models/alpsalpine_skrp.stp
4.60 x 2.50 x 3.20 mm
