Embeetle/tiny-scarab/3d_models/D_SOD-323-bidirectional.step

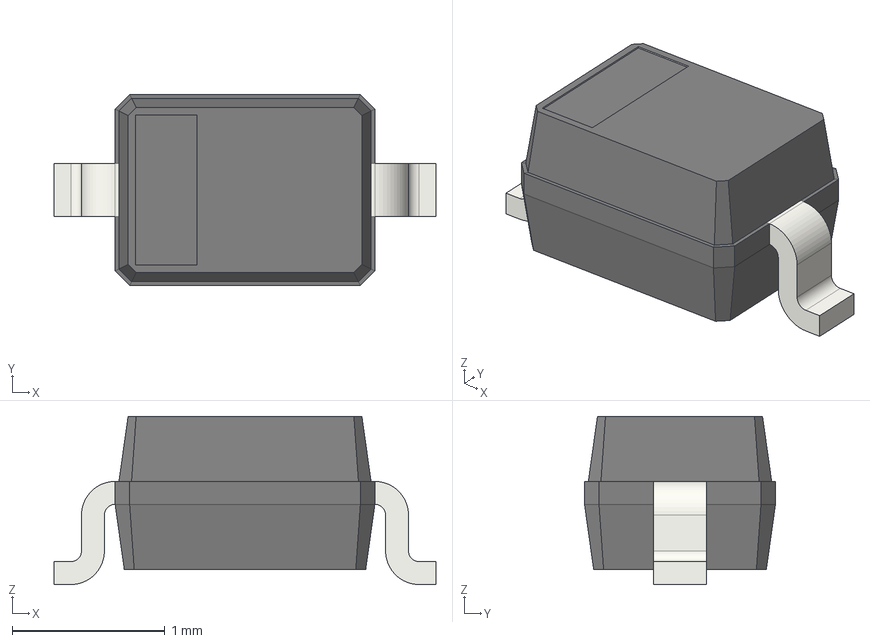
[picture p126: CAD file, 2024-01-21]
3d_models/D_SOD-323-bidirectional.step
2.50 x 1.25 x 1.10 mm
