Embeetle/tiny-scarab/3d_models/ss-12sdp2.stp

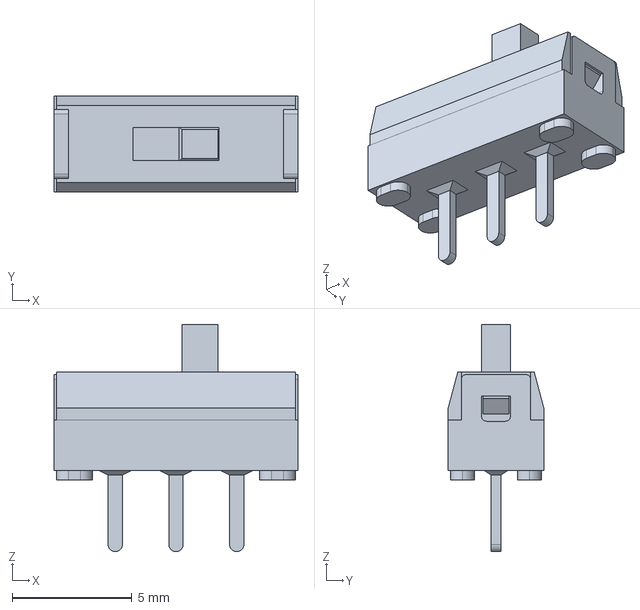
[picture p127: CAD file, 2024-01-13]
3d_models/ss-12sdp2.stp
10.2 x 4.00 x 9.50 mm
