Embeetle/tiny-scarab/3d_models/USB4110GFA.step

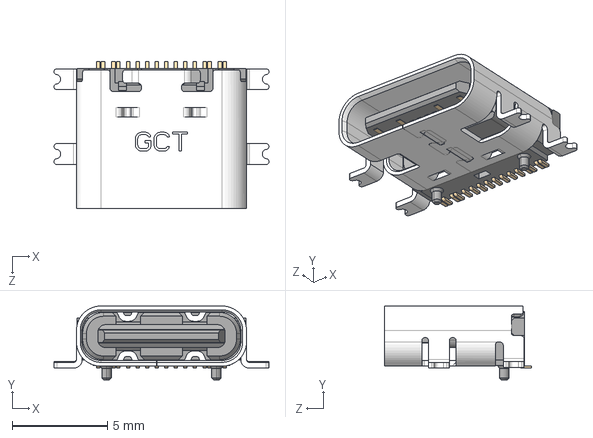
[picture p128: CAD file, 2024-01-13]
3d_models/USB4110GFA.step
11.3 x 3.89 x 7.70 mm
