Embeetle/tiny-scarab/3d_models/ECS-240-20-30B-TR.step

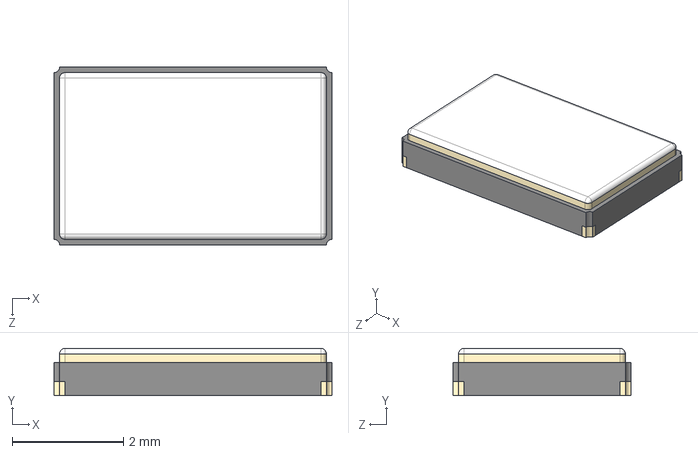
[picture p129: CAD file, 2024-01-13]
3d_models/ECS-240-20-30B-TR.step
5.00 x 0.85 x 3.20 mm
