Embeetle/tiny-scarab/flash_debug_probe_firmware/soldered_resistor.png

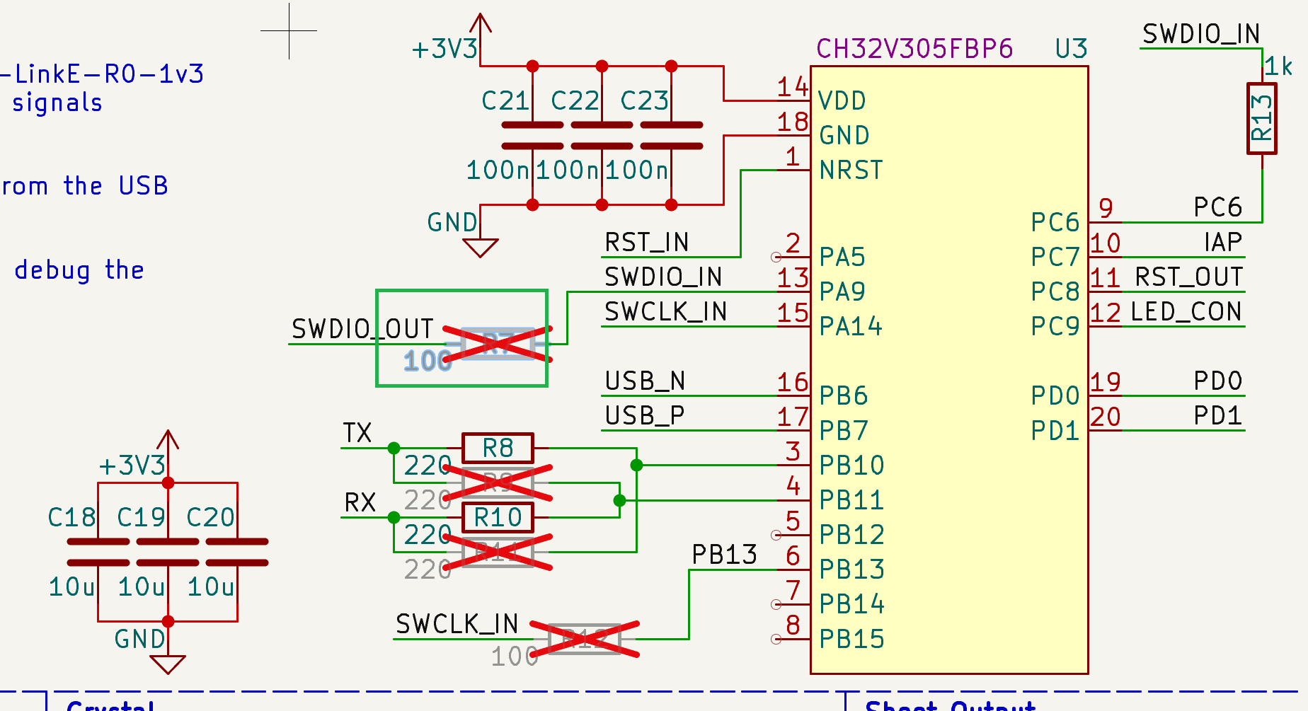
flash_debug_probe_firmware/soldered_resistor.png
