Embeetle/tiny-scarab/documentation/website_figures/flash_debug_01.webp

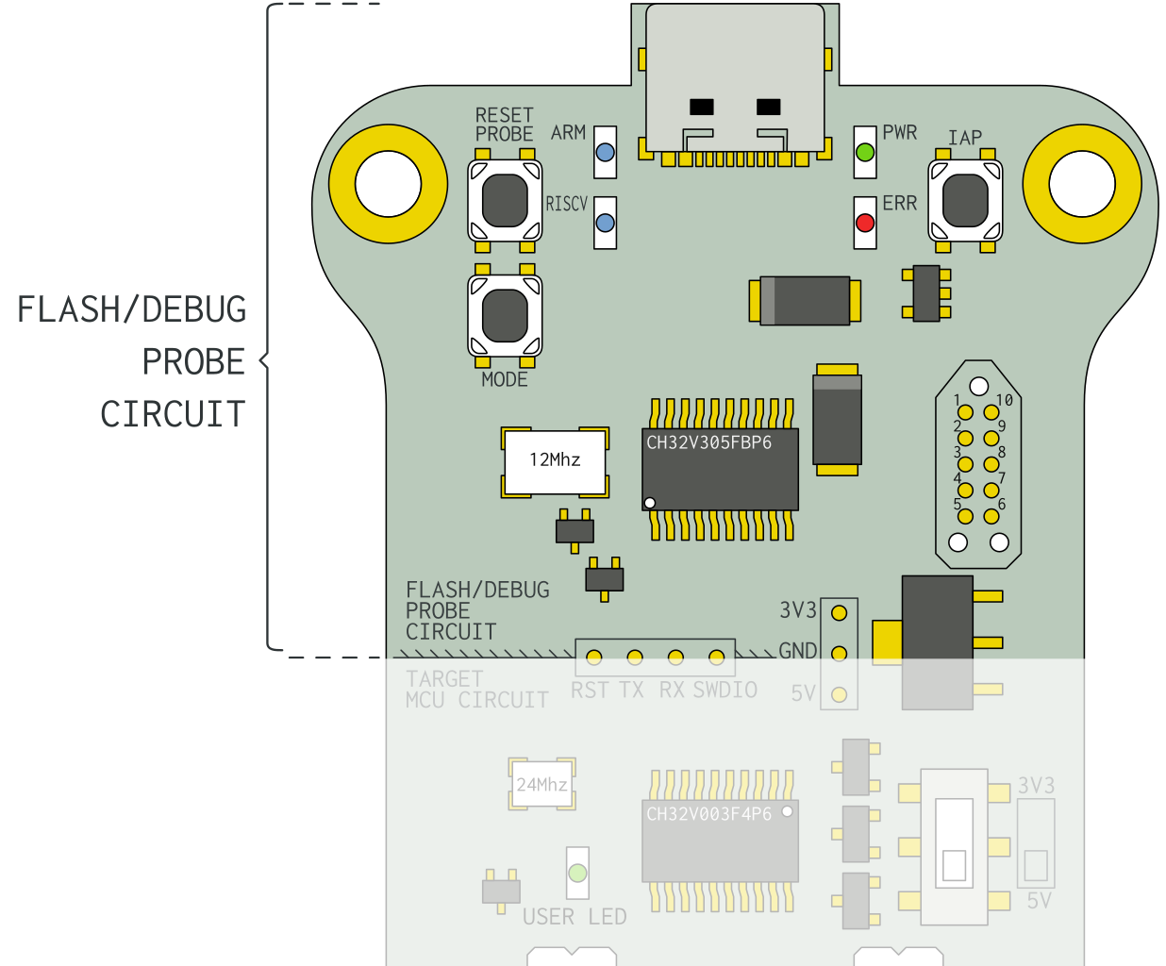
documentation/website_figures/flash_debug_01.webp
