Embeetle/tiny-scarab/flash_debug_probe_firmware/tag_connect.png

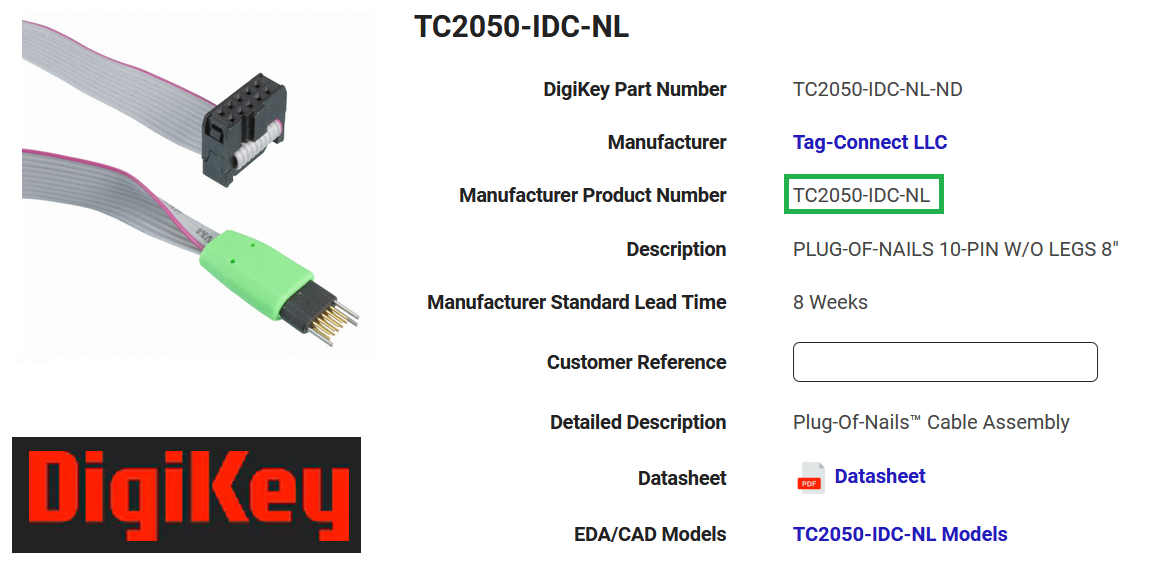
flash_debug_probe_firmware/tag_connect.png
